jh2802/wompler/source/streams_generator_i2sexperiment227/logtable.h

#pragma once
const int8_t logtable[128]={0,23,32,39,
45,51,55,60,64,68,72,75,78,82,85,88,91,93,96,99,101,104,106,109,111,113,115,118,120,122,124,126,128,130,132,134,136,138,139,141,143,145,147,148,150,152,153,155,157,158,160,162,163,165,166,168,169,171,172,174,175,177,178,180,181,182,184,185,187,188,189,191,192,193,195,196,197,199,200,201,202,204,205,206,207,209,210,211,212,213,215,216,217,218,219,221,222,223,224,225,226,227,229,230,231,232,233,234,235,236,237,238,239,241,242,243,244,245,246,247,248,249,250,251,252,253,254,255,};

const int8_t logtableb[128] {0,0,0,0,0,0,0,0,0,0,1,1,1,1,1,1,1,2,2,2,2,2,3,3,3,3,4,4,4,4,5,5,5,6,6,6,7,7,7,8,8,9,9,9,10,10,11,11,12,12,13,13,14,14,15,15,16,16,17,18,18,19,19,20,21,21,22,23,23,24,25,25,26,27,27,28,29,30,30,31,32,33,34,34,35,36,37,38,39,40,40,41,42,43,44,45,46,47,48,49,50,51,52,53,54,55,56,57,58,59,60,61,62,63,65,66,67,68,69,70,71,73,74,75,76,78,79,80};
const int16_t SIN1024_DATA []   = {-1, 6, 12, 18, 25, 31, 37, 43, 50,
56, 62, 69, 75, 81, 87, 94, 100, 106, 113, 119, 125, 131, 138, 144, 150, 157,
163, 169, 175, 182, 188, 194, 201, 207, 213, 219, 226, 232, 238, 245, 251, 257,
263, 270, 276, 282, 289, 295, 301, 307, 314, 320, 326, 332, 339, 345, 351, 358,
364, 370, 376, 383, 389, 395, 402, 408, 414, 420, 427, 433, 439, 446, 452, 458,
464, 471, 477, 483, 490, 496, 502, 508, 515, 521, 527, 533, 540, 546, 552, 559,
565, 571, 577, 584, 590, 596, 603, 609, 615, 621, 628, 634, 640, 646, 653, 659,
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
3239, 3245, 3251, 3257, 3264, 3270, 3276, 3282, 3288, 3294, 3301, 3307, 3313,
3319, 3325, 3331, 3337, 3344, 3350, 3356, 3362, 3368, 3374, 3381, 3387, 3393,
3399, 3405, 3411, 3417, 3424, 3430, 3436, 3442, 3448, 3454, 3460, 3467, 3473,
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
 }; 
