jh2802/wompler/source/streams_generator_i2sexperiment227/sqlw.h

#pragma once

const int16_t sqlw[16384]={0,128,181,221,256,286,313,338,362,384,404,424,443,461,478,495,512,527,543,557,572,586,600,613,627,640,652,665,677,689,701,712,724,735,746,757,768,778,789,799,809,819,829,839,
849,858,868,877,886,896,905,914,923,931,940,949,957,966,974,983,991,999,1007,1015,1024,1031,1039,1047,1055,1063,1070,1078,1086,1093,1101,1108,1115,1123,1130,1137,1144,1152,1159,1166,1173,1180,1187,1193,
1200,1207,1214,1221,1227,1234,1241,1247,1254,1260,1267,1273,1280,1286,1292,1299,1305,1311,1317,1324,1330,1336,1342,1348,1354,1360,1366,1372,1378,1384,1390,1396,1402,1408,1413,1419,1425,1431,1436,1442,
1448,1453,1459,1465,1470,1476,1481,1487,1492,1498,1503,1509,1514,1519,1525,1530,1536,1541,1546,1551,1557,1562,1567,1572,1578,1583,1588,1593,1598,1603,1608,1614,1619,1624,1629,1634,1639,1644,1649,1654,
1659,1664,1668,1673,1678,1683,1688,1693,1698,1702,1707,1712,1717,1722,1726,1731,1736,1740,1745,1750,1755,1759,1764,1768,1773,1778,1782,1787,1792,1796,1801,1805,1810,1814,1819,1823,1828,1832,1837,1841,
1846,1850,1854,1859,1863,1868,1872,1876,1881,1885,1889,1894,1898,1902,1907,1911,1915,1920,1924,1928,1932,1936,1941,1945,1949,1953,1958,1962,1966,1970,1974,1978,1982,1987,1991,1995,1999,2003,2007,2011,
2015,2019,2023,2027,2031,2035,2039,2043,2048,2051,2055,2059,2063,2067,2071,2075,2079,2083,2087,2091,2095,2099,2103,2107,2111,2114,2118,2122,2126,2130,2134,2138,2141,2145,2149,2153,2157,2160,2164,2168,
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
5132,5134,5135,5137,5139,5140,5142,5143,5145,5147,5148,5150,5151,5153,5155,5156,5158,5159,5161,5163,5164,5166,5167,5169,5170,5172,5174,5175,5177,5178,5180,5182,5183,5185,5186,5188,5189,5191,5193,5194,
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
